JaimeDeArcos/IMUs---VR/0.documents/1.reference-articles/Andrés Jaramillo - Transformaciones espaciales.pdf

DESCRIPCIONES Y TRANSFORMACIONES ESPACIALES

© Andrés Jaramillo Botero, 2005 | 1

# Descripciones y Transformaciones Espaciales

2

### Tabla de Contenido

1.1. DESCRIPCIÓN DE UBICACIÓN ESPACIAL: SISTEMAS COORDENADOS,

### Lista de Ejemplos

EJEMPLO 4 DETERMINACIÓN DEL EJE Y ÁNGULO DE ROTACIÓN EQUIVALENTES A PARTIR DE

4

### Lista de Ejercicios

EJERCICIO 1 DADO UN VECTOR u = ⎡x y z w ⎣ | ⎤
⎦

T
TRANSFORMADO EN TRANSLACIÓN POR
UN VECTOR ai | b j | c k ⎡
⎣ | ⎤
⎦

T
? | 9

EJERCICIO 2 DADO UN PUNTO u = 3i + 4 j + 5k CUAL ES EL EFECTO DE ROTARLO 90o
ALREDEDOR DEL EJE Z HASTA UN NUEVO PUNTO V ? | 13
EJERCICIO 3 ROTE EL PUNTO V ANTERIOR ALREDEDOR DEL EJE Y α HASTA UN NUEVO PUNTO
W. DEFINA LA ROTACIÓN COMPUESTA, DE MANERA SIMBÓLICA, EN T | 13
EJERCICIO 4 APLIQUE UNA TRANSFORMACIÓN DE ROTACIÓN SOBRE EL RESULTADO ANTERIOR,
T, DE SOBRE SU PROPIO EJE Z, PARA DEFINIR SIMBÓLICAMENTE TN | 15
EJERCICIO 5 SUPONGA UN OBJETO SÓLIDO DE FORMA TRIANGULAR CON VÉRTICES INDICADOS EN LA FIGURA 5. DEFINA LA TRANSFORMACIÓN COMPUESTA QUE REPRESENTE UNA ROTACIÓN DE 90o SOBRE EL EJE Z SEGUIDA DE UNA ROTACIÓN DE 90o SOBRE EL EJE Y SEGUIDA DE UNA TRANSLACIÓN DE 3 UNIDADES EN LA DIRECCIÓN X. ENCUENTRE LOS
VÉRTICES RESULTANTES DEL OBJETO TRANSFORMADO | 15
EJERCICIO 6 SUPONIENDO QUE EL EFECTOR FINAL DE UN MANIPULADOR DEBE ATORNILLAR
UNA TUERCA SOBRE UN EJE DEFINIDO POR EL VECTOR r = ⎡1 2 3 ⎣ | ⎤
⎦

T
. ENCONTRAR LA

MATRIZ DE ROTACIÓN, Rr ,α , QUE REPRESENTA LA ROTACIÓN EN θ RESPECTO DEL
VECTOR | 19
EJERCICIO 7 DETERMINE EL EJE (K) Y ÁNGULO DE ROTACIÓN ( ) EQUIVALENTES PARA LA
MATRIZ | 22
EJERCICIO 8 DESARROLLE LAS TRADUCCIONES ENTRE TRANSFORMADA HOMOGÉNEA Y ÁNGULOS DE EULER (CONVENCIONES X, Y, Y RPY, TRANSFORMADAS HOMOGÉNEAS Y
CUATERNIOS, Y SUS CORRESPONDIENTES TRANSFORMACIONES INVERSAS | 27

### PENDIENTE POR INTEGRAR EL RESTO DE EJERCICIOS

### Lista de Figuras

6

### 2. Mecánica de Cuerpos Rígidos

Un brazo manipulador puede modelarse como un sistema articulado de cuerpos rígidos¹; la localización de cada cuerpo rígido, ligado al manipulador o dentro de su entorno de trabajo, se describe completamente por su posición y orientación en el espacio respecto de un sistema de coordenadas definido. Así mismo, para representar la relación espacial entre los cuerpos que componen un manipulador y de éstos con objetos en su ambiente de trabajo, es necesario establecer descriptores espaciales y operadores de transformación sobre los mismos que permitan expresar el estado en tiempo de las correspondientes posiciones y orientaciones. En este capítulo se presentan las herramientas matemáticas más utilizadas en el campo de la robótica de los manipuladores, principalmente derivadas del álgebra lineal y de la teoría de tornillos² [], para expresar la localización de un cuerpo y la relación espacial entre cuerpos en el espacio en función de las variables de articulación de un brazo manipulador.

1.1. Descripción de ubicación espacial: sistemas coordenados, posiciones y orientaciones

El movimiento de un cuerpo rígido en el espacio se describe dando la localización de un punto particular sobre el mismo en cada instante de tiempo, en relación con un sistema de coordenadas de referencia. Para la descripción de posición y orientación de las partes de un robot manipulador u otros objetos dentro del espacio de trabajo se utilizan sistemas de coordenadas. De manera concreta, se escoge como sistema de coordenadas un conjunto de tres ejes ortogonales³ y se especifica la localización de cada punto del cuerpo rígido mediante un vector de posición utilizando la terna (x, y,z )∈!³ , donde cada coordenada expresa la proyección de la

ubicación del punto seleccionado sobre cada eje. En algunos casos, es necesario definir más de un sistema de coordenadas por lo cual cada vector asociado a un punto en el espacio es etiquetado con información para identificar el sistema de coordenadas dentro del cual está definido (ver Figura 1). En su forma geométrica, una flecha se utiliza para describir el tamaño y la orientación de un vector.

1 Se entiende, idealmente, como cuerpo rígido aquel que no se deforma. En términos más formales, es una colección de partículas organizadas de tal manera que la distancia entre éstas permanece fija, independiente de los movimientos o fuerzas ejercidas sobre el conjunto.
2 Los elementos de la teoría de tornillo se remontan al trabajo de Chasles y Poinsot a principios del siglo diecinueve (1800s).
3 Vectores cuyo producto punto sea cero, uv⋅ = 0 , se dicen ser vectores ortogonales (vectores perpendiculares entre si), y si además son unitarios se dicen ser ortonormales.

1.1.1. Descripción de una posición

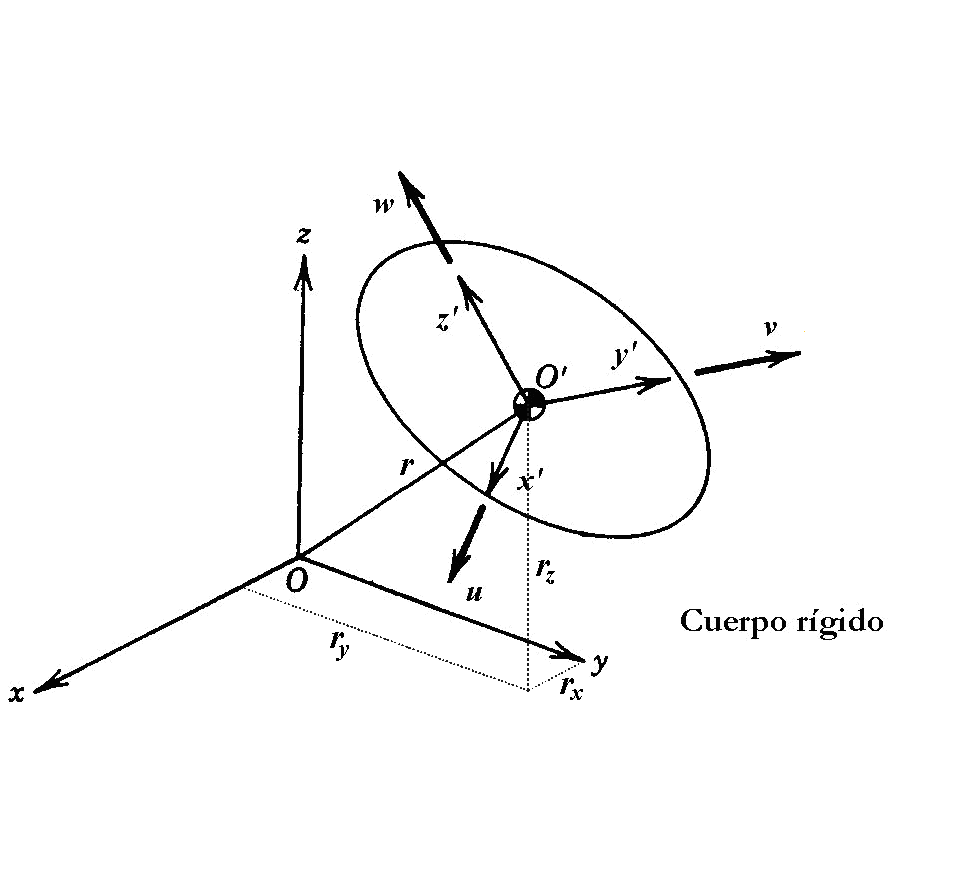
[picture p73: figure]

Figura 1 Posición y orientación de un cuerpo rígido

Una vez definido un sistema de coordenadas de referencia se localiza cualquier punto respecto de éste por medio de un vector de posición de dimensión 3x1. Los componentes numéricos de este vector indican la proyección del mismo sobre los ejes principales del sistema de referencia.

La posición de un objeto en el espacio se representa, de manera usual, por las coordenadas de un punto arbitrario en el espacio. Asumiendo un sistema de coordenadas de referencia Oxyz y un punto arbitrario O' fijado a un cuerpo rígido, como se muestra en la Figura 1, la ubicación de dicho punto respecto del sistema de coordenadas de referencia está dada por el vector columna

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
. | (0.1)
1.1.2. Descripción de una orientación

Para describir la orientación de un cuerpo en el espacio se asigna un sistema de coordenadas ligado al cuerpo (fijo al mismo) y luego se describe la relación espacial entre dicho sistema de coordenadas y el sistema de coordenadas de referencia. Una manera de describir el sistema de coordenadas ligado al cuerpo, es escribir los vectores unitarios de sus ejes principales en términos del sistema de coordenadas de referencia; esto resulta en un vector unitario de dimensión 3x1 para cada eje del sistema de coordenadas ligado al cuerpo. De manera conveniente se pueden expresar los tres vectores unitarios resultantes como las columnas de una matriz de

8

dimensión 3x3. Esta matriz se denomina matriz de rotación porque describe la relación de orientación entre un sistema de coordenadas relativo a otro (en este caso el de referencia). Asumiendo, como se muestra en la Figura 1, un sistema de coordenadas de referencia dado por Oxyz, un sistema de coordenadas ligado a un cuerpo en movimiento dado por O’uvw y los vectores unitarios x', y' y z' apuntando en la dirección de los ejes coordenados u, v, y w respectivamente; la matriz de rotación que expresa la orientación del sistema Ouvw respecto del sistema Oxyz está dada por,

OxuwROxyz

=

x '

x | y '
| x | z ' x
x ' y | y ' y | z ' y
x '
z | y '
| z | z ' z

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
. | (0.2)

Dado que los componentes de cualquier vector unitario son simplemente sus proyecciones sobre las direcciones unitarias del sistema de referencia empleado, cada uno de estos puede escribirse como el producto punto de un par de vectores unitarios. El producto punto de dos vectores unitarios resulta en el coseno del ángulo entre estos, es por ello que los componentes de una matriz de rotación son referidos frecuentemente como cosenos de dirección,
v1 ⋅ v2 = cos(a ) | (0.3)

donde, v1 y v2 son vectores unitarios ∈!³×1 con un mismo origen y a el ángulo entre ellos.

Consecuentemente, los escalares, r
ij , en (0.2) pueden expresarse de la siguiente manera,

OxyzRO'x ' y'z ' =

x '⋅ x y '⋅ x z '⋅ x
x '⋅ y y '⋅ y z '⋅ y
x '⋅z y '⋅z z '⋅z

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
(0.4)

Se identifica cada vector columna de la matriz de rotación en (0.4), como la proyección de los ejes principales del sistema de coordenadas en movimiento O'x'y'z' sobre cada uno de los ejes principales del sistema de referencia Oxyz. Por inspección de la ecuación (0.4) se evidencia que los vectores fila de la matriz de rotación equivalen a los vectores unitarios de Oxyz expresados en O'x'y'z'. Entonces, la descripción del marco Oxyz con relación al marco O'x'y'z' está dada por la traspuesta de (0.4). Es decir,

O'x ' y'z '

ROxyz = OxyzRO'x ' y'z '
T | (0.5)

Esto sugiere que la inversa de una matriz de rotación básica es igual a su traspuesta, O'x ' y'z '

ROxyz = OxyzRO'x ' y'z '

−1 | = OxyzRO'x ' y'z '
T | , hecho que puede
verificarse teóricamente del álgebra lineal dado que la inversa de una matriz con columnas/filas ortonormales es igual a su traspuesta. Esto se verifica fácilmente como,

O'x ' y'z '
ROxyz
OxyzRO'x ' y'z ' =U3×3 , | (0.6)

donde U3×3 ∈!³×3 corresponde a la matriz de identidad.

Como se verá posteriormente, existen otro tipo de representaciones para describir la orientación de un cuerpo en el espacio.

1.1.3. Descripción de un marco (sistema de coordenadas)

Debido a que la información requerida para describir completamente la ubicación de la mano (o cualquier otro elemento) de un manipulador debe incluir necesariamente un término de posición y otro de orientación, se define por conveniencia una entidad denominada marco que es simplemente un sistema de coordenadas asociado con cada cuerpo rígido que permite expresar dicha información. El punto dentro del cuerpo que se escogerá en adelante para describir la posición de un cuerpo será, también por conveniencia, el origen del sistema de coordenadas ligado a dicho cuerpo.

Sin embargo, comúnmente se integran ambas operaciones en un solo operador. Para ello se utilizan matrices de transformación homogéneas de 4x4 que incluyen operaciones de rotación y traslación del sistema de coordenadas ligado al cuerpo.

Una matriz de rotación de 3x3 no da la posibilidad simultánea de traslación y escalado, por lo tanto se introduce una cuarta coordenada o componente al vector de posición p=(px,py,pz)T en un espacio tridimensional que lo transforma en ⌢
p = (wpx ,wp y ,wpz ,w)

T donde ⌢
p se expresa en coordenadas homogéneas de la siguiente manera,

px = wpx
w , p y =

wp y
w , pz =

wpz
w . | (0.7)

En general la representación de un vector de n componentes con un vector de n+1 componentes se denomina representación en coordenadas homogéneas.

Ejercicio 1 Dado un vector u = ⎡x y z w ⎣ | ⎤
⎦

T
cual es el vector k transformado en translación
por un vector ai | b j | c k ⎡
⎣ | ⎤
⎦

T
?

10

### 1.2. Matrices de Rotación

Figura 2 Rotaciones básicas respecto de los ejes x, y, z

1.1.1. Matrices de Rotaciones Básicas

Suponiendo dos sistemas de coordenadas de orígenes coincidentes, OUVW y OXYZ, y asumiendo que el sistema OUVW se mueve rotacionalmente con respecto al sistema de referencia OXYZ. Se define una matriz de rotación como un operador que expresa la diferencia de orientación entre el sistema de coordenadas en movimiento (OUVW) y el sistema de referencia

x

y

z

u

w

v

cubo
unitario
φ

Plano x-z

φ

wx

z

x | wz

uz

| ux
o | o
p | p

x

y

z

u

w

v

cubo
unitario θ

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
o | o

p

x

y

z

u

w

v | y

z

w

v

Plano y-z

cubo
unitario

vz

vy
wz

wy

α

α o | o

p

p

fijo (OXYZ). Por simplicidad ilustrativa, suponga la presencia de un cuerpo sólido ligado por uno de sus vértices al sistema OUVW en movimiento, es decir, se mueve con él (Figura 2). Representando cualquier punto del cuerpo como un vector p respecto del sistema OUVW, se define entonces la matriz de rotación como aquella que opera sobre p y transforma sus coordenadas expresadas en el sistema de coordenadas rotado OUVW en el sistema de coordenadas de referencia OXYZ.

Es de interés encontrar una matriz que transforme las coordenadas de un punto cualquiera p, ligado a un sistema de coordenadas en movimiento OUVW, a las coordenadas expresadas con respecto al sistema de coordenadas de OXYZ, después de que el sistema de coordenadas OUVW ha sido girado. Es decir, la siguiente transformación ortogonal (ortonormal ya que sus componentes son vectores unitarios):

| | pxyz = Rpuvw | | | (0.8)

Otra posibilidad es la de expresar un punto ligado al sistema de coordenadas OXYZ en términos del sistema de coordenadas en movimiento OUVW. Esta transformación se expresa de la siguiente manera,

| | puvw = Qpxyz | | | (0.9)
Como | los | productos | escalares | son | conmutativos,
QR = RTR = R⁻¹
R =U3×3 (donde U es una matriz de identidad de 3x3), siendo Q = R⁻¹ = RT .

Definición de los componentes de un vector :

| | puvw = pu i u + pv
i
| | | v + pwkw | | (0.10)

donde pu , pv y pw son las proyecciones de p sobre los ejes principales del sistema de coordenadas OUVW e iu , jv , kw son vectores unitarios sobre los ejes de OUVW.

Utilizando la definición del producto escalar entre dos vectores a y b y el
ángulo α que los separa, a ⋅b = | a | b cosα (o a ⋅b = cosα cuando a y b
son vectores unitarios) y la ecuación (0.10),
| px = i

### x ⋅ p = i

| | x ⋅i u pu + i

x ⋅ j

| | | v pv + i x ⋅kw pw

p y = j y ⋅ p = j y ⋅i

u pu + j y ⋅ j

v pv + j y ⋅kw pw

pz = kz ⋅ p = kz ⋅i

u pu + kz ⋅ j

| | | v pv + kz ⋅kw pw

Por propiedad, el producto escalar es conmutativo, es decir a ⋅b = b ⋅ a , por lo tanto reescribiendo las ecuaciones anteriores de forma matricial

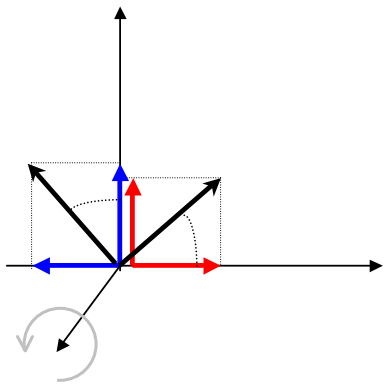
[picture p74: figure]

12

R =

i

x ⋅i
u i

x ⋅ j
v i

x ⋅kw
j y ⋅i
u | j y ⋅ j
v | j y ⋅kw
kz ⋅i
u | kz ⋅ j
v | kz ⋅kw

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
, | (0.11)

y utilizando las identidades relacionadas con la naturaleza periódica del seno y el coseno para simplificar el valor angular,
sen(θ ) = −sen(−θ ) = −cos θ + 90o
( | ) = cos θ − 90o
( | )

cos(θ ) = cos(−θ ) = sen θ + 90o

( | ) = −sen θ − 90o
( | ) | (0.12)

se puede entonces derivar las matrices de rotación con respecto a cada eje rotado, de la siguiente manera: Pxyz = Rx,α Puvw , donde Rx,α corresponde a una rotación respecto del eje x en un ángulo α . En este caso se observa que i x≡ i u ya que no cambian después de la rotación (ver Figura 3).

Figura 3 Matriz de rotación básica, Rx,α,

Rx ,α =

i

x ⋅i
u i

x ⋅ j
v i

x ⋅kw
j y ⋅i
u | j y ⋅ j
v | j y ⋅kw
kz ⋅i
u | kz ⋅ j
v | kz ⋅kw

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
1 | 0 | 0
0 cos(α) −sen (α)
0 sen (α) cos(α)

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
. | (0.13)

Igualmente,

R y,φ =

i

x ⋅i
u i

x ⋅ j
v i

x ⋅kw
j y ⋅i
u | j y ⋅ j
v | j y ⋅kw
kz ⋅i
u | kz ⋅ j
v | kz ⋅kw

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
cos(φ) 0 sen (φ)

0 | 1 | 0
−sen (φ) 0 cos(φ)

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
, | (0.14)

Rz ,θ =

i

x ⋅i
u i

x ⋅ j
v i

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
cos(θ ) −sen (θ ) 0
sen (θ ) cos(θ ) 0
0 | 0 | 1

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
. | (0.15)

kz · kw

jy · kw =-

jy · jv =cosα

kz· jv =senα
y

x=u

z

α

v

w

Estas son las matrices de rotaciones básicas. Pueden ser multiplicadas entre si para representar una secuencia de rotación finita respecto al sistema de referencia; pero como la multiplicación de matrices no conmuta es importante el orden de realización de las rotaciones.

Las matrices representadas en (0.13), (0.14) y (0.15) pueden deducirse fácilmente a partir de la

Figura 2. El componente proyectado de un vector unitario (de magnitud 1) equivale al coseno o seno del ángulo en cuestión, a partir de la definición de los mismos, cara opuesta = 1 ⋅ cos(φ) y cara adyacente = 1 ⋅ sen(φ).

Ejemplo 1 Rotación básica sobre un eje principal

Suponiendo un punto poxyz = ⎡1 2 3 ⎣ | ⎤
⎦

T
expresado con respecto del sistema OXYZ y asumiendo que el sistema de coordenadas OUVW ha sido rotado con respecto del eje X un ángulo de 30º, el mismo punto expresado en términos del sistema de coordenadas OUVW estaría dado por:

pouvw = Rx ,30⁰

T ⋅ poxyz

p ouvw

1
0
0

0
cos( 30.grd)
sen( 30.grd)

0
sen( 30.grd)
cos( 30.grd)

1
2
3

p ouvw

1
3.232
1.598

=

fin Ejemplo 1

Ejercicio 2 Dado un punto u = 3i + 4 j + 5k cual es el efecto de rotarlo 90o alrededor del eje z hasta un nuevo punto v ?

Ejercicio 3 Rote el punto v anterior alrededor del eje y α hasta un nuevo punto w. Defina la rotación compuesta, de manera simbólica, en T.

1.1.2. Rotaciones Compuestas

Para representar una secuencia finita de rotaciones se pueden multiplicar las matrices de rotación básica entre sí, observando cuidadosamente el orden o secuencia de realización de las rotaciones. Este orden es importante dado que la multiplicación de matrices no es conmutativa. Cada matriz de rotación dentro de la secuencia puede expresar una transformación

14

rotacional respecto del sistema de coordenadas de referencia fijo (en los casos anteriores denominado OXYZ) o respecto de alguno de los ejes del sistema de coordenadas en movimiento (OUVW). Para obtener un orden adecuado en la secuencia de multiplicaciones partiendo de la coincidencia entre ambos sistemas de coordenadas observe las siguientes reglas:

### 1. Defina una matriz identidad de 3x3 para representar la

coincidencia entre los dos sistemas de coordenadas.

### 2. Si el sistema de coordenadas en movimiento (OUVW) se

gira respecto de uno de los ejes principales del sistema de referencia (OXYZ), entonces premultiplicar la matriz de rotación previa resultante por la matriz de rotación básica correspondiente a dicho giro.

### 3. Si el sistema de coordenadas en movimiento (OUVW) se

gira respecto de alguno de sus ejes, entonces postmultiplique la matriz de rotación previa resultante por la matriz de rotación básica correspondiente a dicho giro.

Ejemplo 2 Rotación compuesta

Encontrar la matriz de rotación resultante que representa la siguiente secuencia de giros:

### 1. Giro de 80° respecto del eje OX

### 2. Giro de 35° respecto del eje OZ

### 3. Giro de 15° respecto del eje OU

### 4. Giro de 30° respecto del eje OY

R xu(α)

1
0
0

0
cos(α)
sen(α)

0
sen(α)
cos(α)

R yv(φ)

cos(φ)
0
sen(φ)

0
1
0

sen(φ)
0
cos(φ)

R zw(θ )

cos(θ )
sen(θ )
0

sen(θ )
cos(θ )
0

0
0
1

R yv( 30.

grd ) R zw( 35.

grd ) . | R xu( 80.
grd ) . | R xu( 15.

grd ) .

0.709
0.574
0.41

0.541
0.071
0.838

0.451
0.816
0.361

=

Para comprobar que la secuencia es importante, se verifica a continuación como cambia el resultado si no se tuviese en cuenta la no-conmutabilidad en la multiplicación de matrices,

R xu( 80.grd ) R zw( 35.grd ) . | R xu( 15.grd ) . | R yv( 30.grd ) .

0.635
0.58
0.51

0.554
0.117
0.824

0.538
0.806
0.247

=

Ejercicio 4 Aplique una transformación de rotación sobre el resultado anterior, T, de sobre su propio eje z, para definir simbólicamente Tn.

Ejercicio 5 Suponga un objeto sólido de forma triangular con vértices indicados en la Figura 5. Defina la transformación compuesta que represente una rotación de 90o sobre el eje z seguida de una rotación de 90o sobre el eje y seguida de una translación de 3 unidades en la dirección x. Encuentre los vértices resultantes del objeto transformado.

Figura 4 Sólido triangular referido en Ejercicio 5

{1,0,0,1}

{1,4,0,1}

{-1,4,0,1}

{-1,0,2,1}

{1,0,2,1} {-1,0,0,1}

x

y

z

16

fin Ejemplo 2

1.1.3. Rotación Sobre un Eje Arbitrario

En algunos casos se hace necesario representar giros del sistema de coordenadas en movimiento OUVW sobre ejes arbitrarios. Por ejemplo, suponiendo que se quiere mover la mano de un robot manipulador sobre un eje arbitrario dentro de su volumen de trabajo (espacio de trabajo alcanzable por el manipulador) con el propósito de insertar una tuerca en un tornillo. Se define el eje de giro de rosca del tornillo como el eje arbitrario y se representa este por medio de un vector unitario con componentes r = rx ,r y ,r ( z ) que pasa por el mismo origen del sistema de

coordenadas de la mano del robot.

Para derivar la matriz de rotación compuesta resultante se puede llevar a coincidencia cualquiera de los ejes principales del sistema de coordenadas OUVW con el vector r a través de una secuencia de rotaciones sobre los ejes principales del sistema de coordenadas OXYZ, luego se gira con respecto al mismo eje llevado a coincidencia (o r) en un ángulo correspondiente al giro requerido respecto de r y finalmente se regresa a la posición original el sistema de coordenadas girado. Matemáticamente esto se puede expresar de la siguiente manera a partir de un ejemplo.

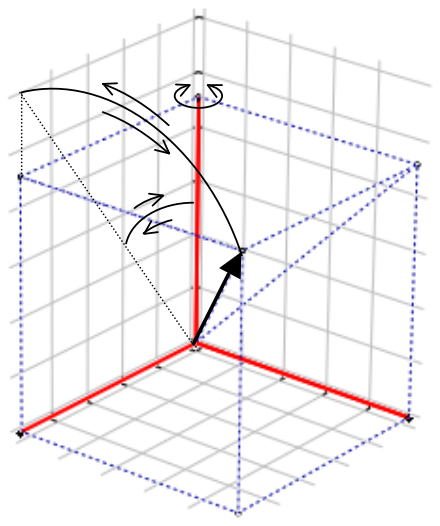
[picture p75: figure]

Figura 5 Rotación respecto de un eje arbitrario r

El primer paso es definir el eje que se llevará a coincidencia con r.

Arbitrariamente se escoge el eje z (podría ser cualquiera de los otros). De la Figura 5 se deduce que,

z

y x

r

α

β

θ

rx | ry

rz

❶

❺
❷

❸

❹

18

sen(α) = r y
r y

2 + r
z
2 | cos(α) = | r z
r y
| | 2 + r z
| | 2
sen(β) = | rx
rx

2 + r y

2 + r
z
2 | cos(β) = | r ² − rx
| | 2
rx
| | 2 + r y 2 + r
z

2 = r y

2 + r
z

2

rx

2 + r y

2 + r
z

2

El siguiente paso es definir la secuencia de giros que llevarán a coincidencia los vectores unitarios r y OZ.

Rr ,φ = Rx ,−α ⋅R y,β ⋅Rz ,θ ⋅R y,−β ⋅Rx ,α

La matriz de rotación compuesta resultante puede expresarse en términos del vector r así,

Rr ,φ =

cφ r y

2 + r
z

2

( ) + rx
2

r

2

rx r y r Vφ − sφ r

2
r
z
r

3

rx r

z r Vφ + sφ r

2
r y
r

3

rx r y r Vφ + sφ r

2
r
z
r

3

cφ rx

2 + r
z

2

( ) + r y
2

r

2

r y

r

z r Vφ − sφ r

2
rx
r

3

rx r

z r Vφ − sφ r

2
r y
r

3

r y

r

z r Vφ + sφ r

2
rx
r

3

cφ rx

2 + r y
2

( ) + r

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
donde, cφ = cos(φ), sφ = sen(φ) , Vφ = 1− cos(φ) y el vector r no

requiere ser expresado como vector unitario.

Simplificando los términos diagonales,

Rr ,φ = 1
r

2

rx

2

Vφ + r

2
cφ rx r y

Vφ − sφ r r
z rx r
z

Vφ + sφ r r y

rx r y

Vφ + sφ r r
z r y

2

Vφ + r

2
cφ r y
r
z

Vφ − sφ r rx

rx r
z

Vφ − sφ r r y r y
r
z

Vφ + sφ r rx r
z

2

Vφ + r

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
(0.16)

Donde

Ejemplo 3 Rotación sobre un eje arbitrario

Gire un cuerpo ligado al sistema OUVW en un ángulo de 35° respecto de un vector r

oxyz = (1,1,1).

Aplicando la ecuación (0.16) para un vector r y un ángulo de rotación de 35 grados,

R x( 35.grd, r)

0.879
0.391
0.271

0.271
0.879
0.391

0.391
0.271
0.879

=

fin Ejemplo 3

La ecuación (0.16) representa una transformación muy útil que será utilizada posteriormente.

Ejercicio 6 Suponiendo que el efector final de un manipulador debe atornillar una tuerca sobre un eje
definido por el vector r = ⎡1 2 3 ⎣ | ⎤
⎦

T
. Encontrar la matriz de rotación, Rr ,α , que representa la rotación en θ respecto del vector .

### 1.1.3.1. Ángulo y Eje de Rotación Equivalente

Dada una transformación rotacional arbitraria, se puede utilizar la ecuación
(0.16) para obtener el eje sobre el cual una rotación equivalente de φ se lleva a cabo. Dada una transformación rotacional R expresada simbólicamente por los ejes ortogonales en movimiento (vectores columna) sobre los ejes principales xyz (vectores fila):

R =

nx | ox | a x
n y | oy | a y
nz | oz | az

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
Se iguala R con Rr ,φ en la ecuación (0.16) para encontrar relaciones trigonométricas que permitan deducir φ a partir de funciones seno y coseno.

nx | ox | a x
n y | oy | a y
nz | oz | az

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
Vφ + r

2
cφ rx r y

Vφ − sφ r r
z rx r
z

Vφ + sφ r r y

rx r y

Vφ + sφ r r
z r y

2

Vφ + r

2
cφ r y
r
z

Vφ − sφ r rx

rx r
z

Vφ − sφ r r y r y
r
z

Vφ + sφ r rx r
z

2

Vφ + r

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
(0.17)

De este procedimiento, y asumiendo una rotación positiva alrededor del vector r de tal forma que 0 ≤ φ ≤ π , se encuentra que el ángulo de rotación está definido de manera única como:

φ = atan2 nx + oy + az ( | −1), oz − a ( y )
2

### + ax − n ( z )

2

+ ny − o ( x ) ⎛ | 2
⎝

⎜

⎞
⎠

⎟ . (0.18)

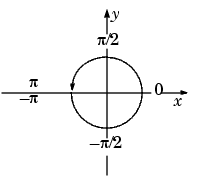
[picture p76: figure]

20

Donde la función atan2 corresponde a la tangente inversa con rango ampliado entre ⎡−π ⎣ ,π) (ver Figura 6).

Figura 6 Rangos de la función atan2 (⎡−π ⎣ ,π) )

Este resultado se obtiene a partir de la ecuación (0.17) sumando los elementos diagonales para determinar una expresión cos(φ) y de la

diferencia entre los términos simétricos respecto a la diagonal elevados al cuadrado para determinar la expresión sen(φ). Es decir,

cφ =

nx + oy + az −1
2 | (0.19)

### sφ = ¹

2

oz − a ( y )
2

### + ax − n ( z )

2

### + ny − o ( x )

2
| (0.20)

Los componentes de r pueden obtenerse de igual manera como

rx = oz − a y
2sen (φ) | (0.21)

r y = a x − nz
2sen (φ) | (0.22)

r

z = n y − ox
2sen (φ) | (0.23)

Cuando el ángulo de rotación es muy pequeño, el eje de rotación no está físicamente bien definido debido a la magnitud de los denominadores y numeradores en las ecuaciones (0.21)-(0.23). Cuando el ángulo de rotación se acerca a 180o el vector r tampoco está bien definido debido a la magnitud del seno.

Para ángulos mayores de 90o se procede de manera diferente a encontrar el vector r, igualando los elementos diagonales de la ecuación (0.17) para encontrar el elemento más grande de r. Se presume que la matriz de rotación está normalizada y su determinante es +1 para sistemas dextrogiro (regla de la mano derecha - RMD) o -1 para sistemas levogiro.

(Mirar forma de 0.16)

rx = signo oz − a ( y ) nx − cos(φ)
1− cos(φ) | (0.24)

r y = signo a x − n ( z ) oy − cos(φ)
1− cos(φ) | (0.25)

r

z = signo n y − o ( x ) az − cos(φ)
1− cos(φ) | (0.26)

Si rx es el más grande,

r y =

n y + ox
2rx
Vφ | (0.27)

r

z =

a x + nz
2rx
Vφ | (0.28)

Si r y es el más grande,

rx =

n y + ox
2r y
Vφ | (0.29)

r

z =

oz + a y
2r y
Vφ | (0.30)

Si r
z es el más grande,

rx =

a x + nz
2r
z
Vφ | (0.31)

r y =

oz + a y
2r
z
Vφ | (0.32)

Ejemplo 4 Determinación del eje y ángulo de rotación equivalentes a partir de una matriz de rotación dada.

22

Determine el eje (k) y ángulo de rotación (θ ) equivalentes para la matriz.

R y,90Rz ,90 =

0 0 1
1 0 0
0 1 0

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
De la ecuación (0.18) encontramos

θ = atan2

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
= 120o

Siendo θ > 90o se determina el componente más grande de k correspondiente al elemento más grande de la diagonal.

| kx = 1/ 2 3/ 2 = 1
| 3

Entonces,
| ky = 1
| 3 kz = 1
| 3

Es decir, R y,90oRz ,90o = Rk,120o donde k = 1
| 3 i +
| 1
| 3 j +
| 1
| 3 k

fin Ejemplo 4

Ejercicio 7 Determine el eje (k) y ángulo de rotación ( ) equivalentes para la matriz

Rz ,90R y,90 =

0 −1 0 0
0 0 1 0
−1 0 0 0
0 0 0 1

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
1.1.4. Operadores de Rotación con Ángulos de Euler y Cuaternios

Figura 7 Representación gráfica de los ángulos de Euler (convención x)

Las matrices de rotación básicas expresadas por los operadores (0.13),
(0.14) y (0.15) requieren de nueve elementos para describir parcialmente la orientación de un cuerpo rígido rotante respecto de un sistema de coordenadas de referencia. Además, individualmente no conducen directamente a un conjunto completo de coordenadas generalizadas.

Tal conjunto de coordenadas generalizadas pueden ser proporcionados por los denominados ángulos de Euler φ, θ y ψ.

Existen múltiples secuencias de rotación posibles con estos tres ángulos, sin embargo, en la práctica se utilizan con mayor frecuencia las convenciones RPY (“Roll-Pitch-Yaw”), X y Y (para la cuales la rotación intermedia se da sobre el eje respectivo mencionado). A continuación se presentan las matrices correspondientes a dichas convenciones,

Rz ,φR y,θRx ,ψ =

### cφcθ cφsθsψ − sφcψ cφsθcψ + sφsψ sφcθ sφsθsψ + cφcψ sφsθcψ − cφsψ

−sθ | cθsψ | cθcψ

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
(0.33)

z,z¹

y

x x¹

y¹

y

x x¹,

φ

φ

z² | y²
θ

y

x x¹,x²

φ

z²,z3 | y²
θ

ψ

y³

x³

z,z¹

z,z¹

24

Rz ,φRx ',θRz ',ψ =

### cφcψ − sφcθsψ −sφcθcψ − cφsψ sφsθ sφcψ + cφcθsψ cφcθcψ − sφsψ cφsθ

sθsψ | sθcψ | cθ

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
(0.34)

Rz ,φR y',θRz ',ψ =

### sφsψ − cφcθcψ −cφcθsψ − sφcψ cφsθ cφsψ + sφcθcψ −sφcθsψ + cφcψ sφsθ

−sθcψ | sθsψ | cθ

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
(0.35)

1.1.5. Cuaternios

Uno de los problemas en el uso de los ángulos de Euler es que conducen a singularidades cuando el movimiento angular se acerca a 0⁰ o a 180⁰. Sin embargo, empleando cuaternios y álgebra de cuaternios es factible evitar dichas singularidades. Los cuaternios, definidos por Hamilton [HAM1843], pueden ser empleados para representar transformaciones de giros y orientaciones. Un cuaternio está constituido por cuatro componentes
variables q0 , q1 , q2 , q ( | 3 ) que representan sus coordenadas en una base
{h, i, j ,k} . El cuaternio se constituye de un término escalar, h, y tres que conforman una parte vectorial, {i, j ,k} . De este modo un cuaternio puede

representarse como:
Q = q0 , q1 , q2 , q ( | 3 ) = (s,v) | (0.36)

donde, s corresponde a un valor escalar y v a un vector.

### 1.1.5.1. Propiedades de los Cuaternios

El conjugado de Q → Q* se define mantiendo el signo de s e invirtiendo el de v.
Q* = q0 ,−q1 ,−q2 ,−q ( | 3 ) = (s,−v) | (0.37)

El producto de dos cuaternios Q1 ⋅ Q2 está dado por, Q3 = Q1 ⋅ Q2 = s1 ,v1 ( )⋅ s 2 ,v 2 ( ) = s1
| s 2 − v1 T v 2 ,v1 × v 2 + s1

v 2 + s 2

v ( | 1 ) (0.38)

Es de notar que el producto entre cuaternios no es generalmente conmutativo.

La suma de dos cuaternios Q1 + Q2 se define como,
Q3 = Q1 + Q2 = s1 ,v1 ( ) + s 2 ,v 2 ( ) = s1 + s 2 ,v1 + v 2 ( | ) | (0.39)

El producto por un escalar Q2 = aQ1 se define como,
Q2 = aQ1 = a s1 ,v1 ( ) = as1 , av1 ( | ) | (0.40)

La norma | Q | está dada por,
| | Q⋅ Q* = q0 2 + q1

2 + q2

2 + q3
2
( | ) h | (0.41)

El inverso para un cuaternio Q , no nulo, se define por, Q⁻¹ = Q*
Q | (0.42)

La composición de rotaciones utilizando cuaternios resulta de la multiplicación entre cuaternios.

El cuaternio que representa una rotación de valor θ sobre un eje r está dada por,

Q = R (r ,θ ) = cos

θ
2

⎛
⎝

⎜

⎞
⎠

⎟ ,r ⋅sen

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
⎟ | (0.43)

Ejemplo 5 Rotaciones empleando cuaternios
El cuaternio que representa una rotación de 90⁰ sobre un eje (4, 2,−1) está

dada por,

Q = R r ,90⁰

( ) = 2
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
Para aplicar dicha rotación sobre otro vector l se evalúa el producto Q⋅(0, l)⋅ Q*

fin Ejemplo 5

Rotaciones compuestas pueden expresarse fácilmente por medio del producto entre cuaternios,

Q3 = Q2 ⋅ Q1 | (0.44)

Ejemplo 6 Composición de rotaciones con traslaciones

PONER EJEMPLOS NUMERICOS

El resultado de trasladar por un vector p seguido por rotar Q el sistema OXYZ es un nuevo sistema OUVW, donde las coordenadas del vector r en el sistema OXYZ, definidas en OUVW, son,

0,r ( oxyz ) = Q⋅ 0,r ( ouvw )⋅ Q* + (0, p) | (0.45)

26

Aplicando primero el giro y después la traslación,
0,r ( oxyz ) = Q⋅ 0,r
ouvw ( + p)⋅ Q* | (0.46)

Manteniendo el sistema OXYZ fijo y trasladando r un vector p, seguido de una rotación Q, se obtiene r’ de coordenadas,
0,r ' ( oxyz ) = Q⋅ 0,r
oxyz ( + p)⋅ Q* | (0.47)

Mientras la operación de rotación seguida de la traslación resulta en,
0,r ( oxyz ) = Q⋅ 0,r ( oxyz )⋅ Q* + (0, p) | (0.48)

fin Ejemplo 6

Estas cuatro variables expresadas en términos de los ángulos de Euler se denominan cuaternios y están dadas por,

q0 = sen

θ
2

cos

φ −ψ
2 | (0.49)

q1 = sen

θ
2

sen

φ −ψ
2 | (0.50)

q2 = cos

θ
2

sen

φ +ψ
2 | (0.51)

q3 = cos

θ
2

cos

φ +ψ
2 | (0.52)

Donde la condición de normalización está dada por,

qn

2 = 1 n=0

3
∑ | (0.53)

La relación entre los cuaternios y la matriz de orientación R está dada por,

Rii = q3

2 + qi

2 − q j
2

j≠i

∑ | (0.54)

Rij = 2qi

q j + ε ijkq3

qk | i ≠ j | (0.55)

Donde i=0,1,2.

En forma matricial,

R =

qx

2 − q y

2 − qz

2 + q3

2 | 2qx q y + 2q3
qz | 2qx qz − 2q3
q y
2qx q y − 2q3

qz −qx

2 + q y

2 − qz

2 + q3
2 2q y

qz + 2q3
qx
2qx qz + 2q3
q y 2q y

qz − 2q3

qx −qx

2 − q y

2 + qz

2 + q3
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
(0.56)

Ejercicio 8 Desarrolle las traducciones entre Transformada Homogénea y Ángulos de Euler (convenciones X, Y, y RPY, Transformadas Homogéneas y Cuaternios, y sus correspondientes transformaciones inversas

FALTA INCLUIR TRANSFORMACIONES EQUIVALENTES!!

1.1.6. Interpretación Geométrica de las Matrices de Rotación [Fu]

Falta Enunciado ¡!

- Cada vector columna es una representación del vector unitario del eje rotado expresado en términos de los vectores unitarios de los ejes del sistema de referencia, y cada vector fila es una representación del vector unitario de los ejes de referencia expresado en función de los vectores unitarios de los ejes rotados del sistema OUVW.
- Como cada fila y columna es una representación de un vector unitario, la magnitud de cada una de ellas debería ser igual a 1 (Sistema de coordenadas ortonormal). El determinante de una matriz de rotación es +1 para un sistema dextrogiro (RMD) y -1 para un levogiro (sentido opuesto a RMD).
- Como cada fila es una representación vectorial de vectores ortonomales, el producto interno (producto escalar) de cada fila por cualquier otra fila es igual a cero. Lo anterior se cumple de manera análoga para el producto interno entre columnas.
- La inversa de una matriz de rotación es la traspuesta de sí misma. Esto se deduce a partir de las primeras dos observaciones anteriores.

### 1.3. Matrices de Transformación Homogéneas

Las matrices de rotación únicamente permiten representar cambios de orientación entre dos sistemas de coordenadas diferentes. En robótica de manipuladores es evidente la necesidad de representar cambios traslacionales, además de los rotacionales. Para ello se definen las matrices de transformación homogénea.

Una matriz de transformación homogénea es un operador que soporta ambas transformaciones de manera integrada, además de escalado y perspectiva. Son matrices de 4x4 que transforman un vector expresado en

28

coordenadas homogéneas desde un sistema de coordenadas hasta otro sistema de coordenadas. Consisten de 4 submatrices.

T = Rotacion3x 3 | Posicion3x1
perspectiva1x 3 | escalado1x1

⎡
⎣
⎢ | ⎤ ⎦
⎥ | (0.57)

La submatriz superior derecha tiene el efecto de trasladar el sistema de coordenadas OUVW que tiene ejes paralelos al sistema de referencia OXYZ, pero cuyo origen está en el punto Posición3x1. La submatriz superior izquierda corresponde al operador de rotación que relaciona la orientación entre dos sistemas de coordenadas. La submatriz inferior izquierda se emplea para variaciones en la perspectiva visual de los elementos y la submatriz inferior derecha corresponde a un parámetro de escalado (ambos empleados en aplicaciones de simulación y modelado).

1.3.1. Transformaciones de Perspectiva

Figura 8 Transformación de Perspectiva

Suponiendo la imagen formada de un objeto visto a través de un lente, un punto del objeto x, y, z se visualiza en las coordenadas x’

, y’

, z’ si el lente
tiene una distancia focal f positiva. y’ representa la distancia de imagen y varía de acuerdo con la distancia del objeto y. Si dibujamos puntos en un plano perpendicular al eje y localizado en y’ (como el plano de filmación de una cámara), se forma entonces una imagen en perspectiva.

Un rayo que pase por el centro del lente no se desvía, por lo tanto, se puede escribir,

z
y

= z '
y ' | (0.58)

x
y

= x '
y ' | (0.59)

Un rayo pasante y paralelo al lente pasa a través del punto focal f, por lo tanto,

z
f

= z '
y '+ f | (0.60)

f

x,y,z

x’,y’,z’

y

x

z

x
f

= x '
y '+ f | (0.61)

Nótese que x’, y’, y z’ son negativos y f es positivo. Eliminando y’ entre las ecuaciones (0.58) y (0.60) se obtiene,

z
f

= z '
z ' y
z

+ f ⎛
⎝

⎜

⎞
⎠

⎟

(0.62)

y resolviendo por z’ se obtiene,

z ' = | z
1− y f | (0.63)

A partir de las ecuaciones (0.59) y (0.61) se obtiene,

x ' = | x
1− y f | (0.64)

Para obtener la distancia y’ se reescriben las ecuaciones (0.58) y (0.60) de la siguiente manera,

z
z '

= y
y ' | (0.65)

z
z '

= f
y '+ f | (0.66)

Por lo tanto,

y
y '

= f
y '+ f | (0.67)

y

y ' = y
1− y f | (0.68)

La transformación homogénea que produce el mismo efecto es,

P =

1 | 0 | 0 0
0 | 1 | 0 0
0 | 0 | 1 0
0 − 1
| f | 0 1

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
(0.69)

30

Dado que cualquier punto xi + y j + z k se transforma de la siguiente manera,

x
y
z
1− y
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
1 | 0 | 0 0
0 | 1 | 0 0
0 | 0 | 1 0
0 − 1
| f | 0 1

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
(0.70)

el punto de la imagen x’, y’, z’ obtenido dividiendo por el factor de peso (1− y / f ) , es

x
(1− y / f )
i + | y
(1− y / f ) j + | z
(1− y / f )
k | (0.71)

Una transformada similar a P pero con –1/f en la posición 4,1 o 4,3 produce una transformación en perspectiva a lo largo del eje x o a lo largo del eje z, respectivamente.

1.3.2. La Transformación de Escalado

Esta transformación es útil, en modelado y simulación, para representar deformaciones. Sin embargo, no son comunes. Para representar escalado heterogéneo a lo largo de cada uno de los ejes principales se emplearía la siguiente transformación,

T =

a 0 0 0
0 b 0 0
0 0 c 0
0 0 0 1

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
(0.72)

Donde, a, b, c representan los factores de escalado en x, y, z respectivamente. Para escalado homogéneo de un objeto por un factor s, s = a = b = c en (0.72).

Referencias

1. B. Roth, “Performance Evaluation of Manipulators from a Kinematic Viewpoint”, Performance Evaluation of Manipulators, National Bureau of Standards, special publication, 1975.
2. D. Pieper, “The Kinematics of Manipulators Under Computer Control” Unpublished Ph.D. thesis, Stanford University, 1968.
3. H.Y., Lee y C.G., Liang, “Displacement Analysis of the General Spatial 7-Link 7R Mechanism.” Mechanism and Machine Theory, 23, 219-226, 1998.
4. R.G., Selfridge, “Analysis of 6-Link Revolute Arms”, Mechanism and Machine Theory, 24 (1), 1-8, 1989.
5. C., Mavroidis, y B., Roth, “Structural Parameters Which Reduce the Number of Manipulator Configurations”, Journal of Mechanical Design, 116, 3-10, 1994.
6. J., Duffy, “Analysis of Mechanisms and Manipulators”, John Wiley & Sons, 1980.
7. M., Raghavan y B., Roth, “Inverse kinematics of Manipulators Under Computer Control”, Proceedings 2nd International Congress for the Theory of Machines and Mechanisms, Zakopane, Poland. Vol. 2. 159-
168. 1993.
8. R.P., Paul, Robot Manipulators: Mathematics, Programming and Control, MIT Press, 1981.
9. D.E. Whitney, “Resolved Motion Rate Control of Manipulators and Human Prosthesis”, IEEE Transactions on Man-Machine Systems, 10(2), 47-53, 1969.
10. R.M. Murray, Z. Li, y S.S. Sastry, A Mathematical Introduction to Robotic Manipulation, London: CRC Press, 1994.
11. S. Y., Nof, ”Handbook of Industrial Robotics”, 2nd Ed., John Wiley & Sons, New York, 1999.
12. R.C. Dorf, S. Y., Nof, “International Encyclopedia of Robotics: Applications and Automation”, Vol. 1-3, John Wiley & Sons, New York, 1988.
13. K.S. Fu, R.C. González y C.S.G. Lee, “Robótica: Control, Detección, Visión e Inteligencia”, McGraw-Hill, España, 1988.
14. Barrientos, L.F. Peñin, C. Balaguer, R. Aracil, “Fundamentos de Robótica”, McGraw-Hill, España, 1998.

32

Glosario de Términos

Indice

A

atan2, 20
C

cosenos de dirección, 8
L

localización, 6
M

matriz de rotación, 8
O

ortogonales, 6, 19
R

relación espacial, 6, 7
Robot Stanford, 31
Rotaciones Compuestas, 13

S

sistema de coordenadas, 6, 7, 8, 9, 10, 11, 13, 14, 17, 23, 28
T

Transformaciones Espaciales Ángulos de Euler, 23
Cuaternios, 23, 24, 25, 26 Conjugado de, 24
Inverso de, 25
Norma de, 25
Producto de, 24
Producto por un escalar, 24 Suma de, 24
Escalado, 30
Matrices de rotación básica, 10
matriz de transformación homogénea, 27 Perspectiva, 28
Rotación, 10, 13, 14, 17, 18, 19, 23, 27
V

vector, 6, 7, 8, 9, 11, 13, 17, 18, 19, 21, 24, 25, 26, 27
vector de posición, 7
