JaimeDeArcos/IMUs---VR/0.documents/1.reference-articles/Francisco Dominguez - Filtro Complementario DCM.pdf

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

## Contents

1 Introducción | 3
2 Construción de la DCM con Acelerómetro y Brújula | 3
3 Relación entre el Giróscopo y la DCM | 7
4 Construcción de la DCM con Acelerómetro y Giróscopo | 8

5 Construcción de la DCM con Acelerómetro, Brújula y Girós-
copo | 9
6 Correción de los valores de la DCM | 10

2

## 1 Introducción

A continuación vamos a mostrar un algoritmo de fusión de sensores inerciales basado en la técnica de ltros complementarios, utilizando como representación de conversión de sistemas de referencias o sistemas de coordenadas las Matrices de Cosenos Directores.
| Partimos de la consideración de que tenemos herramientas de medida inercial
calibradas y con valores correctos. Las herramientas de medida inercial son normalmente tres:
1. Giróscopo, mide la velocidad ángular del dispositivo.
2. Acelerómetro, mide la aceleración asociada al dispotivo, incluida la gravedad,
| que es la que nos interesa para determinar la orientación.
3. Brújula o magnetómetro, que mide los campos magnéticos, incluido el de
| la tierra, que es el que nos interesa para determinar la orientación

Todas estas herramientas nos devuelven tres valores de medida, es decir miden en los tres ejes de coordenadas.
| El objetivo es obtener la matriz de cosenos directores que convierte medidas
del sistema global al sistema del cuerpo o local. En nuestro caso el sistema global será el sistema de referencias de la tierra donde:
| El norte es el eje X descrito con el vector I. El oeste es el eje Y descrito con el vector J El cielo es el eje Z descrito con el vector K.

En la gura 1 se ilustra nuestro sistema de referencia global que es el de la tierra:

En cuanto al sistema de referencia del cuerpo o local, vamos a considerar nuestro dispositivo de medida, donde todos los sensores están perfectamente alineados entre si, vease la gura 2.

## 2 Construción de la DCM con Acelerómetro y Brújula

El caso más sencillo y por el que comenzaremos a fusionar medidas de dispotivos, consiste en unir las medidas del acelerometro y la brújula.
| Los acelerómetros miden la gravedad, el vector de gravitación apunta hacia el
centro de la tierra y es opuesto al vector que apunta al cielo en nuestro caso −→KB.

Considerando que los valores de nuestro acelerometro los representamos con el

| 3

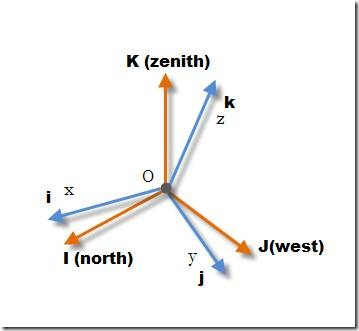
[picture p77: figure]

Figure 1: Sistema de referencia global o de la tierra

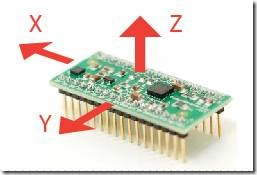
[picture p78: figure]

Figure 2: Sistema de referencia local o del cuerpo

4

vector −→A = {Ax, Ay, Az} y considerando que no hay aceleraciones externas

debidas a otras fuerzas, podemos asumir que:

−→KB = −

−→A | (1)

Es decir que el vector de dirección −→K que es el del eje de coordenadas Z del

sistema de referencia global, tienes unos valores de coordenadas en el sistema de referencias local o del cuerpo −→KB dados por −

−→A, es decir los valores medidos

en el acelerometros cambiados de signo.
Por otro lado, si disponemos de una brujula corregida y calibrada correctamente, esta nos proporciona un vector de medida −→M = {Mx, My, Mz} que esta

siempre orientado al norte con lo que coincide con el vector director del eje X del sistemas de coordenadas global o de la tierra en este caso, con lo que tenemos:

−→IB =

−→M | (2)

Es decir, −→IB es el vector director del eje de coordenadas X del sistema de

coordenadas de la tierra expresado en coordenadas locales o del cuerpo.
Ya sabemos que conocidos −→IB y

−→KB el eje vector de dirección de coordenadas

o versor para el eje Y viene determinado por el producto vectorial de los dos vectores anteriores:

−→JB =

−→KB ⊗

−→IB = {−AyMz + AzMy, −AxMz + AzMx, −AxMy + AyMx} (3)

De esta forma teniendo los valores del acelerometro y el magnetómetro podemos construir nuestra matríz de cosenos directores. Que vendria expresada como:

[

−→IB,

−→JB,

−→KB] =

Mx | −AyMz + AzMy | −Ax
My | −AxMz + AzMx | −Ay
Mz | −AxMy + AyMx | −Az
- = DCMB | (4)

Esta matriz nos permitiría saber las coordenadas locales o del cuerpo de cualquier vector expresado en coordenadas globales o de la tierra. Es decir dado −→rB podemos determinar −→rG.
Pero lo que estamos buscando es la orientación de nuestro dispositivo, cuerpo, con respecto a las coordenadas globales, de la tierra o a nosotros. Normalmente los vectores que nos van a dar una idea de la orientación de nuestro cuerpo serán los vectores directores de los ejes de coordenadas de nuestro sistema de referencia −→i ,

−→j ,

−→k , que vienen dados por los valores:

| −→iB = {1, 0, 0} T
(5)
| −→jB = {0, 1, 0} T
(6)
| −→kB = {0, 0, 1} T
(7)

5

Es decir queremos saber o calcular los anteriores vectores expresados en coordenadas del sistema de referencia de la tierra. Para estos o cualquier otro vector −→rB aplicaremos la expresión:

−→rG =

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
−→I ·
−→i

−→I ·
−→j

−→I ·

−→k
−→J ·
−→i

−→J ·
−→j

−→J ·

−→k
−→K ·
−→i

−→K ·
−→j

−→K ·

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
- = DCMG−→rB (8)

Necesitamos calcular DCMG a partir de la conocida DCMB, para ello utilizaremos la igualdad:

DCMG = (DCMB)
T
(9)

Con lo que nos queda:

[

−→iG,

−→jG,

−→kG] =

Mx | My | Mz
−AyMz + AzMy | −AxMz + AzMx | −AxMy + AyMx
−Ax | −Ay | −Az
- = DCMG

(10)
recordemos que:

[

−→iG,

−→jG,

−→kG] = [−→IB,
| −→JB, −→KB]
T = DCMG | (11)

No hace falta realizar la multiplicación de 8 ya que directamente vemos los valores de los vectores que deseamos calcular:

−→iG = {i
G
x

, iG
y

, iG
z }

T = {

−→I ·

−→i , −→J ·

−→i , −→K ·
−→i }
T =

Mx
−AyMz + AzMy
−Ax
- (12)

−→jG = {j
G
x

, jG
y

, jG
z }

T = {

−→I ·

−→j , −→J ·

−→j , −→K ·
−→j }
T =

My
−AxMz + AzMx
−Ayx
- (13)

−→kG = {k
G
x

, kG
y

, kG
z }

T = {

−→I ·

−→k , −→J ·

−→k , −→K ·

−→k }
T =

Mz
−AxMy + AyMx
−Az
- (14)

Si estos sensores no estuviesen afectados por los ruidos o por fuerzas externas para el caso del acelerómetro o campos magnéticos externos para el caso de la brujula, con los resultados obtenidos seria suciente para determinar la orientación del sistema local, cuerpo o dispositivo sensor. Pero esto no ocurre en la realidad, de hecho el dispositivo más preciso y menos ruidoso de los tres de que disponemos es el giróscopo, la causa de esto es principalmente que el giróscopo no se ve afectado por .elementos externos como el caso de fuerzas

6

externas para el acelerómetro o campos magnéticos para la brújula, por lo que su inclusión/fusión en los valores de la DCM resulta muy necesario. Seguidamente vamos a establecer la relación entre el giroscopo y la matriz de cosenos directores y a continuación vamos a fusionar los datos de la DCM anteriores con el giróscopo, para obtener una estimación de la orientación menos ruidosa y más precisa. Comenzaremos integrando acelerómetro y giróscopo y posteriormente añadiremos la brújula.

## 3 Relación entre el Giróscopo y la DCM

El giróscopo nos proporciona la velocidad angular del cuerpo al que esta conectado. Los valores de su medida nos vienen proporcionados como un vector−→wg = {wx, wy, wz} de velocidades angulares para caja eje del sistema local. Estas medidas no nos proporcionan información de la orientación del dispositivo en valores absolutos como lo hacen los dos otros dispositivos, si no que nos determinan cuanto cambia en cada instante de tiempo t.
Vamos a expresar la matriz de cosenos directores en función del tiempo de tal forma que la DCM en el tiempo t la vamos a denotar por DCM(t) y en un instante de tiempo posterios dt, indicaremos DCM(t + dt).
Una importante consideración a tener en cuenta es que las medidas de −→wg nos vienen dadas en el sistema de referencia local o del cuerpo,DCMB , por lo que es en este sistema donde vamos a realizar los calculos, para posteriormente pasar al sistema de referencia global, de tierra o nuestro, DCMG.
Supongamos que en un tiempo determinado tenemos estos valores locales:

DCMB(t) = [−→IB(t),

−→JB(t),

−→KB(t)] | (15)

Transcuridos un tiempo dt tendremos los valores:

DCMB(t + dt) = [−→IB(t + dt),

−→JB(t + dt),

−→KB(t + dt)] | (16)

Tenemos que establecer la relación entre DCMB(t+dt) y DCMB(t) a partir de los valores de −→wg. Para ello nos vamos a centrar en uno de los vectores que forman la matriz y aplicaremos las ecuaciones de la velocidad angular de tal forma que para −→KB(t) tenemos:

−→KB(t+dt) = −→KB(t)+vdt =

−→KB(t)+(−→wg⊗

−→KB(t))dt =

−→KB(t)+dθg⊗

−→KB(t) (17)

donde dθg = −→wgdt ya que dada la velocidad angular −→wg al cabo de un tiempo dt abremos obtenido un cambio en el ángulo dθg.
De manera análoga para los otros dos ejes:

−→IB(t + dt) = −→IB(t) + vdt =

−→IB(t) + (−→wg ⊗

−→IB(t))dt =

−→IB(t) + dθg ⊗

−→IB(t) (18)

−→JB(t + dt) = −→J (t) + vdt =

−→JB(t) + (−→wg ⊗

−→JB(t))dt =

−→JB(t) + dθg ⊗

−→JB(t) (19)

7

Normalmente una de los tres vectores puede calcularse a partir de los otros dos, en nuestro caso el J:

−→JB(t + dt) = −→KB(t + dt) ⊗

−→IB(t + dt) | (20)
4 | Construcción de la DCM con Acelerómetro y

## Giróscopo

Lo comentado en el apartado anterior nos permitiría, partiendo de una inicial correcta DCM(0), calcular la evolución duranten el tiempo DCM(t) para cualquier instante t. Pero esto no es viable en la realidad ya que esta formulación de ir sumando valores nos acumula los errores, hasta que transcurrido un tiempo relativamente corto, los valores de la DCM no coinciden con los reales. Por lo que ahora es necesario fusionar estos valores de la DCM tomados a partir del giróscopo con los valores proporcionados por los otros sensores. En esta sección vamos a comenzar con la fusíón del giroscopo y el acelerómetro.
Una forma sencilla de realizar la fusión es mediante la tecnica de Filtro Complementario o Media Ponderada, para ello necesitamos a calcular tanto −→wg como −→wa, donde este último es la velocidad angular medida. Para esto último utilizaremos los valores del acelerómetro que, como ya sabemos, vienen determinados por:

−−−→KBA(t) = −

−→A(t) | (21)

Antes de seguir debemos realizar una diferenciación entre:

−−−→KBA(t) que es el valor del vector estimado a partir de los valores del

acelerómetro.

−−−→KBG(t) que es el valor del vector estimado a partir de los valores del

giroscomo, tal y como se mostro en la sección anterior.

−→KB(t) que es el valor del vectro total estimado fusionando los dos valores

anteriores.

Para estimar la velocidad angular a partir de los valores de la aceleración utilizamos las ecuaciones del cálculo de velocidad angular dada una velocidad lineal:

−→wa =

−→KB(t) ⊗ va

−→KB(t)|
2

(22)

sabiendo que la velocidad lineal viene dada por:

va =

−−−→KBA(t + dt) −

−→KB(t)
dt | (23)

y que |

−→KB(t)|
2 = 1 dado que los vectores dirección son unitarios.

8

Una vez obtenida la velocidad angular a partir de la aceleración resulta sencillo calcular el incremento del ángulo:

dθa = −→wadt = (−→KB(t)⊗va)dt = (−→KB(t)⊗

−−−→KBA(t + dt) −

−→KB(t)
dt | )dt =

−→KB(t)⊗(

−−−→KBA(t+dt)−

−→KB(t))

(24)
Ahora vamos a calcular la variación o incremento de ángulos estimato total a partir de una media ponderada de los dos valores anteriores.

dθ =

sadθa + sgdθg
sa + sg

(25)

donde los valores de sa y sg son los pesos asociados a ambas estimaciones y se suelen estimar experimentalmente, aunque los valores de sa suelen ser inferiores a los de sg ya que a corto plazo los valores del giroscopo son más precisos, y cuando este no aporta, es decir cuando se para el dispotivo, ya que en ese caso no hay velocidad angular, se tienen más en cuenta los de la aceleración.
Una vez obtenido el incremento del ángulo solo nos queda actualizar el vector:

−→KB(t + dt) = −→KB(t) + dθ ⊗

−→KB(t) | | (26)

del mismo modo se atualizaran el recto de vectores:

−→IB(t + dt) = −→IB(t) + dθ ⊗

−→IB(t) | (27)

−→JB(t + dt) = −→JB(t) + dθ ⊗

−→JB(t) | (28)
5 | Construcción de la DCM con Acelerómetro,

## Brújula y Giróscopo

En este caso el proceso es muy parecido al anterior, donde ahora estimaremos dθmproporcionada por los datos de la brújula o magnetómetro. Como ya sabemos los datos proporcionados por la brújula vienen dados en el vector −→M = {Mx, My, Mz} y proporcionan los datos para el eje global X con el vector

de dirección:

−→IB =

−→M | (29)

Ahora la estimación del incremento del ángulo viene dada por:

dθm = −→wmdt = (−→IB(t) ⊗ vm)dt = (−→IB(t) ⊗

−−→IBM(t + dt) −

−→IB(t)
dt | )dt | (30)

donde nalmente tenemos:

dθm =

−→IB(t) ⊗ (

−−→IBM(t + dt) −

−→IB(t)) | | (31)

9

El suguiente paso es el único que es algo más diferente a los anteriores ya que vamos a fusionar tres valores mediante media ponderada:

dθ =

sadθa + sgdθg + smdθm
sa + sg + sm

(32)

Al igual que antes sm < sgpara que de nuevo ténga más peso a corto plazo y mientras haya movimiento el giróscopo.
Las expresiones de las actualizaciones de los ejes serían las mismas que en el apartado anterior.

## 6 Correción de los valores de la DCM

En la practia despues de haber calculado DCM(t + dt) obtenemos un pequeño error debido a que todos los cálculos han sido realizados considerando que dt es muy pequeño, de tal forma que a mayor valor de dt mayor será el error de estimación de los valores de la matriz. Además este error se va acumulando en cada iteracción del algoritmo.
De tal forma que si los vectores que formanDCM(t) son correctos y cumplen la propiedad de una matriz de rotación, que recordamos que es que los vectores son ortogonales y unitarios. Después de realizar los calculos no podemos decir lo mismo de DCM(t + dt), aunque el error es muy pequeño debido a que normalmente dt es pequeño, es conveniento corregir lo máximo posible los valores, después de cada iteración, para que estos errores no se acumulen.
A continuación vamos a ver unos conceptos básicos que nos servirán como base para realizar los calculos de corrección.

6.1 Asegurar que dos vectores son ortogonales
Consideremos que tenemos dos vectores −→a y
| −→b que son casi ortogonales, es decir

el ángulo que forman ambos esta muy próximo a 90º, pero no es exactamente 90º. Queremos calcularun vector −→b
| 0 que es perpendicular a −→a y esta en el
mismo plano que forman −→a y
| −→b . Tal vector como sabemos peude ser calculado
de forma sencilla mediante el producto vectorial de tal forma que −→c = −→a ⊗

−→b ,

en la gura 3 se ilustra lo indicado.
Como vemos y dadas las propiedades del producto vectorial −→c es perpendicular al plano formado por −→a y a
| −→b . Tambén vemos que −→b
| 0 seria perpendicular
al plano formado por −→a y −→c , mientras que por otro lado
| −→b 0 pertenece al plano

formado por −→a y

| −→b . Para calcular nuestro vector −→b 0 podemos volver a aplicar
el producto vectorial de tal forma que se cumple que −→b
| 0 = −→c ⊗ −→a .
6.2 | Concepto de vector corrección
En la gura anterior vemos que hay un vector más, −→d , del que aun no hemos

hablado, este vector se denomina vector corrección.

10

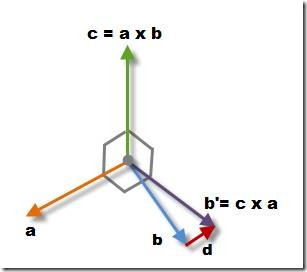
[picture p79: figure]

Figure 3: Calculo de −→b
0

como una modicación de −→b a partir de −→a

Si recordamos los pasos realizados en la sección anterior tenemos que: −→b
0 = −→c ⊗ −→a = (−→a ⊗
−→b ) ⊗ −→a | (33)

Aplicando la regla del triple producto que recordamos a continuación:

(−→c ⊗

−→b ) ⊗ −→a =

−→b (−→c · −→a ) − −→a (−→c ·

−→b ) | (34)
y considerando que −→a · −→a = |−→a | = 1,tenemos que:

(−→a ⊗

−→b ) ⊗ −→a = −−→a (−→a ·

−→b ) + −→b (−→a · −→a ) = −→b +

−→d | (35)

donde −→d = −−→a (−→a ·

−→b ), precisamente es el vector corrección. Si nos jamos −→a y

−→d son paralelos, en realidad −→d es −→a escalado por el producto escalar de −→a con

−→b que de nuevo vemos que es el coseno del ángulo que forman ambos. ya

que ambos son unitarios, que será proximo a cero ya que ambos vectores son casi perpendiculares. Y es justo ese pequeño valor el que hay que corregir por eso −→d se denomina vector corrector. También podemos observar que cos(−→a ,

−→b ) =
sin(−→b ,

−→b
0
).
Volviendo al valor de

−→b
0
tenemos que:

−→b
0 =

−→b +

−→d | (36)
6.3 | Uso del vector correción

A continuación vamos a mostrar como utilizar el vector corrección para corregir tres vectores, en realidad corregiremos solamente dos y el tercero lo calculamos

11

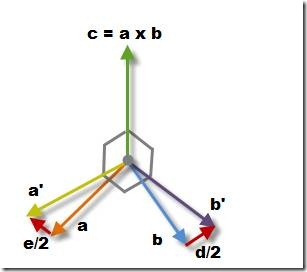
[picture p80: figure]

Figure 4: Corección de dos vectores

a partir del producto vecgorial de los otros dos.
De forma análoga a lo expuesto en el apartado anteror podemos corregir −→a en función de −→b de tal forma que tendriamos que:

−→
a
0 = −→a + −→e | (37)

donde −→e en este caso es −

−→b (−→a ·

−→b ).
Si queremos aplicar las dos correciones a la vez, tanto la de −→a como la de −→b ,

podemos realizar una suposición de que ambos estan igualmente mal y aplicar la mitad de corrección a cada uno de ellos de tal forma que tenemos:

−→
a

0 = −→a −

−→b (−→a ·

−→b )
2 | (38)

−→b
0 =

−→b −

−→a (−→a ·

−→b )
2 | (39)

Vease la gura 4 donde se puede visualizar geométricamente lo comentado anteriormente.
Si denimos una nueva variable Err de la siguiente forma:

Err =

(−→a ·

−→b )
2 | (40)

Tenemos que las dos expresiones anteriores se simplican quedando:

−→
a

0 = −→a − Err ∗

−→b | (41)

12

−→b
0 =
−→b − Err ∗ −→a | (42)

En realidad con el ajuste anterior no se garantiza que

−→
a

0
y

−→b
0
van a ser
ortogonales, pero si van a ser mucho más ortogonales que los originales−→a y

−→b ,

de tal forma que vamos a obtener una mejora en la acumulación de errores.

6.4 Corrección de DCM
Considerando lo anterior, solo nos queda aplicar lo visto a los vectores −→IB(t+dt)

y

−→JB(t + dt). Para ello denimos el error como:

Nota: vamos a eliminar los parametros temporales a los vectores por motivos de claridad y simplicidad.

Err =

(

−→IB ·

−→JB)

2

(43)

y ahora aplicamos las expresiones de coreción:

−→
I

0
B =

−→IB − Err ∗

−→JB‘ | (44)

−→
J

0
B =

−→JB − Err ∗

−→IB | (45)

un paso nal es normalizar y calcular el tercer vector:

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
(46)

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
(47)

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
B | (48)

Estos vectores nales corresponden con nuestra DCM corregida de tal forma que, una vez añadidos los parametros temporales que eliminamos por motivos de claridad y simplicidad, tenemos:

DCMB(t + dt) = [−→
I

00
B(t + dt),

−→
J

00
B(t + dt),

−→
K⁰⁰
B(t + dt)] | (49)

El proceso se repite conforme evoluciona el tiempo, iterándo el algoritmo indenidamente y obteniendo en cada una de ellas una estimación robusta, precisa y estable de la DCM que representa la transformación del sistema de coordenadas local o del cuerpo con respecto al sistema de coorodenadas global, de la tierra o nuestro ya que no sotros solemos observar el cuerpo situados oen la tierra.

13
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
